protogilly/ResistorSortSystem/src/RS_Mainboard/SortWheel.h

/*
SortWheel.h - An object for representing the sortation wheel and its cups
Created by Shawn Westcott (www.8tinybits.com), Feb 2017.

Schematics, Gerbers, and related source code can be found on this project's Github
https://github.com/slwstctt/ResistorSortSystem

This code is currently unlicensed and is only available for educational purposes.
If you'd like to use this code for a non-educational purpose, please contact Shawn
Westcott (shawn.westcott@8tinybits.com).

*/

#ifndef _SORTWHEEL_h
#define _SORTWHEEL_h 1

// Number of Cups on wheel
#define cupCount 10

#include "Arduino.h"
#include <Wire.h>

class SortCup {
	public:
	// Default Constructor -- sets all values to 0 and makes the cup a reject cup
	SortCup();

	// Constructor -- needs a min, max, and nominal. (Not Reject)
	SortCup(double minValue, double maxValue);

	// Constructor -- Min and max are determined via precision (Given as a whole number percentage). (Not Reject)
	SortCup(double nominal, int precision);

	double getMin();
	double getMax();
	bool canAccept(double value);
	bool isReject();
	void setRejectState(bool state);
	void setCupRange(double minValue, double maxValue);
	void setCupRange(double nominalValue, int precisionPercent);

	private:
	double _minVal;
	double _maxVal;
	bool _rejectCup;

};

class SortWheel {
	public:
		// Constructor -- needs the number of cups on the wheel and the Wire channel that the controller is on.
		SortWheel(int numCups, int wireChannel);

		// Returns the current position on the wheel as an integer (First cup is cup 1)
		int getCurrentPosition();

		// Calculates shortest path to the target and issues a command to the controller.
		void moveTo(int target);

		// Collection of cups as part of the SortWheel.
		SortCup cups[cupCount];

	private:
		int _wireChannel;
		int _curPos;
		int _numCups;

};

#endif
